LukeSAV/SDProject/ros_ws/src/rtk/src/ntripclient.cpp

/*
   NTRIP client for POSIX.
   $Id: ntripclient.c,v 1.51 2009/09/11 09:49:19 stoecker Exp $
   Copyright (C) 2003-2008 by Dirk Stöcker <soft@dstoecker.de>

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
 */

/**
 *
 *	@brief This contains the client code for running NTRIP corrections services with an RTK capable device.
 *			
 *	Currently supports Ubuntu devices running ROS. This device uses one USB port for NMEA read and RTCM write.
 *
 *	@author Luke Armbruster
 *
 *	@bug No known bugs.
 */



#include <ctype.h>
#include <getopt.h>
#include <stdio.h>
#include <stdlib.h>
#include <errno.h>
#include <string>
#include <time.h>
#include <chrono>
#include <vector>
#include <numeric>
#include <iostream>
#include <thread>
#include "ros/ros.h"
#include "std_msgs/String.h"
#include "sensor_msgs/NavSatFix.h"
#include "../include/NMEAData.h"
#include "rtk/HeadingSpeed.h"
#include "../include/serial.h"

typedef int sockettype;
#include <signal.h>
#include <fcntl.h>
#include <unistd.h>
#include <arpa/inet.h>
#include <sys/socket.h>
#include <netinet/in.h>
#include <netdb.h>

#define closesocket(sock)       close(sock)
#define ALARMTIME   (2*60)
#define myperror perror

/* The string, which is send as agent in HTTP request */
#define AGENTSTRING "NTRIP NtripClientPOSIX"
#define TIME_RESOLUTION 125

#define MAXDATASIZE 3000 /* max number of bytes we can get at once */

/* CVS revision and version */
static char revisionstr[] = "$Revision: 1.51 $";
static char datestr[]     = "$Date: 2018/12/12 09:49:19 $";

enum MODE { HTTP = 1, RTSP = 2, NTRIP1 = 3, AUTO = 4, UDP = 5, END };

/* */
std::mutex input_buf_lock;
static char input_buf[MAXDATASIZE * 2];
static char buf_to_send[MAXDATASIZE * 2];
static void handleIPConnection(sockettype sockfd);
static int numbytes = 0;

struct Args
{
	const char *server;
	const char *port;
	const char *user;
	const char *proxyhost;
	const char *proxyport;
	const char *password;
	const char *nmea;
	const char *data;
	int         bitrate;
	int         mode;

	int         udpport;
	int         initudp;
	enum SerialBaud baud;
	enum SerialDatabits databits;
	enum SerialStopbits stopbits;
	enum SerialParity parity;
	enum SerialProtocol protocol;
	const char *serdevice;
	const char *serlogfile;
	const char *nmea_usb;
	const char *rtcm_usb;
};

/* option parsing */
#ifdef NO_LONG_OPTS
#define LONG_OPT(a)
#else
#define LONG_OPT(a) a
static struct option opts[] = {
	{ "bitrate",    no_argument,       0, 'b'},
	{ "data",       required_argument, 0, 'd'}, /* compatibility */
	{ "mountpoint", required_argument, 0, 'm'},
	{ "initudp",    no_argument,       0, 'I'},
	{ "udpport",    required_argument, 0, 'P'},
	{ "server",     required_argument, 0, 's'},
	{ "password",   required_argument, 0, 'p'},
	{ "port",       required_argument, 0, 'r'},
	{ "proxyport",  required_argument, 0, 'R'},
	{ "proxyhost",  required_argument, 0, 'S'},
	{ "user",       required_argument, 0, 'u'},
	{ "nmea",       required_argument, 0, 'n'},
	{ "mode",       required_argument, 0, 'M'},
	{ "serdevice",  required_argument, 0, 'D'},
	{ "baud",       required_argument, 0, 'B'},
	{ "stopbits",   required_argument, 0, 'T'},
	{ "protocol",   required_argument, 0, 'C'},
	{ "parity",     required_argument, 0, 'Y'},
	{ "databits",   required_argument, 0, 'A'},
	{ "serlogfile", required_argument, 0, 'l'},
	{0,0,0,0}};
#endif
#define ARGOPT "-d:m:bhp:r:s:u:n:S:R:M:IP:D:B:T:C:Y:A:l:t:e:"

int stop = 0;
int sigstop = 0;
#ifdef __GNUC__
	static __attribute__ ((noreturn)) void sighandler_alarm(
			int sig __attribute__((__unused__)))
#else /* __GNUC__ */
static void sighandler_alarm(int sig)
#endif /* __GNUC__ */
{
	if(!sigstop)
		fprintf(stderr, "ERROR: more than %d seconds no activity\n", ALARMTIME);
	else
		fprintf(stderr, "ERROR: user break\n");
	exit(1);
}

#ifdef __GNUC__
static void sighandler_int(int sig) 
{
	fprintf(stderr, "ERROR: user break\n");
	exit(1);

}
#else /* __GNUC__ */
static void sighandler_alarm(int sig)
{
	sigstop = 1;
	alarm(2);
	stop = 1;
}
#endif /* __GNUC__ */

static void setargs(struct Args *args)
{
	args->server = "insert your ip address here";
	args->port = "10000";
	args->user = "insert your username here";
	args->password = "insert your password here";
	args->nmea = 0;
	args->data = "RTCM3_MAX";
	args->bitrate = 0;
	args->proxyhost = 0;
	args->proxyport = "2101";
	args->mode = NTRIP1;
	args->initudp = 0;
	args->udpport = 0;
	args->protocol = SPAPROTOCOL_NONE;
	args->parity = SPAPARITY_NONE;
	args->stopbits = SPASTOPBITS_1;
	args->databits = SPADATABITS_8;
	args->baud = SPABAUD_57600;
	args->serdevice = 0;
	args->serlogfile = 0;
}

static const char encodingTable [64] = {
	'A','B','C','D','E','F','G','H','I','J','K','L','M','N','O','P',
	'Q','R','S','T','U','V','W','X','Y','Z','a','b','c','d','e','f',
	'g','h','i','j','k','l','m','n','o','p','q','r','s','t','u','v',
	'w','x','y','z','0','1','2','3','4','5','6','7','8','9','+','/'
};

/* does not buffer overrun, but breaks directly after an error */
/* returns the number of required bytes */
static int encode(char *buf, int size, const char *user, const char *pwd)
{
	unsigned char inbuf[3];
	char *out = buf;
	int i, sep = 0, fill = 0, bytes = 0;

	while(*user || *pwd)
	{
		i = 0;
		while(i < 3 && *user) inbuf[i++] = *(user++);
		if(i < 3 && !sep)    {inbuf[i++] = ':'; ++sep; }
		while(i < 3 && *pwd)  inbuf[i++] = *(pwd++);
		while(i < 3)         {inbuf[i++] = 0; ++fill; }
		if(out-buf < size-1)
			*(out++) = encodingTable[(inbuf [0] & 0xFC) >> 2];
		if(out-buf < size-1)
			*(out++) = encodingTable[((inbuf [0] & 0x03) << 4)
				| ((inbuf [1] & 0xF0) >> 4)];
		if(out-buf < size-1)
		{
			if(fill == 2)
				*(out++) = '=';
			else
				*(out++) = encodingTable[((inbuf [1] & 0x0F) << 2)
					| ((inbuf [2] & 0xC0) >> 6)];
		}
		if(out-buf < size-1)
		{
			if(fill >= 1)
				*(out++) = '=';
			else
				*(out++) = encodingTable[inbuf [2] & 0x3F];
		}
		bytes += 4;
	}
	if(out-buf < size)
		*out = 0;
	return bytes;
}

static struct serial rtk_uart; // Serial connection (read/write at 57600)

int main(int argc, char **argv)
{
	ros::init(argc, argv, "rtk_gps_node");
	ros::NodeHandle nh;
	ros::Publisher gpgga_pub = nh.advertise<sensor_msgs::NavSatFix>("rtk_gpgga", 1000);
	ros::Publisher gpvtg_pub = nh.advertise<rtk::HeadingSpeed>("rtk_gpvtg", 1000);

	while(ros::ok()) {
		struct Args args;

		setbuf(stdout, 0);
		setbuf(stdin, 0);
		setbuf(stderr, 0);
		signal(SIGALRM,sighandler_alarm);
		signal(SIGINT,sighandler_int);
		alarm(ALARMTIME);
		setargs(&args);

		FILE *ser = 0;
		char nmeabuffer[200] = "$GPGGA,"; // Start string
		size_t nmeabufpos = 0;
		size_t nmeastarpos = 0;
		int sleeptime = 0;
		const char *rtk_uart_conn = SerialInit(&rtk_uart, "/dev/gps", SPABAUD_57600,
				args.stopbits, args.protocol, args.parity, args.databits, 1);
		
		if(rtk_uart_conn)
		{
			printf("Not connected to RTK device\n");
		}
		do {
			sockettype sockfd = 0;
			struct sockaddr_in their_addr;
			struct hostent *he;
			const char* server;
			const char* port;
			char* b;
			long in_i;
			long out_i;
			char output_buf[MAXDATASIZE];

			char read_buf[MAXDATASIZE];
			int readBytes = 0;

			server = args.server;
			printf("Server: %s\n", server);
			port = args.port;
			printf("Port: %s\n", port);
			memset(&their_addr, 0, sizeof(struct sockaddr_in));
			printf("Waiting for data...\n");


				auto start = std::chrono::system_clock::now();
				auto cur_time = start;
				std::chrono::duration<double> elapsed_time = std::chrono::duration<double>(10.0f); // Initially send message to caster

				std::thread ntrip_thread(handleIPConnection, sockfd); // Launch thread to handle communication with NTRIP server
				numbytes = 0;

				while(true) { // Read Caster data on socket continuously. Send GPGGA message every 5s.
					memset(read_buf, '\0', sizeof(read_buf)); // Clear the buffer
                    input_buf_lock.lock();
					readBytes = SerialRead(&rtk_uart, read_buf, MAXDATASIZE); // Receive any data from the UART hardware buffer
                    input_buf_lock.unlock();

					NMEAData::parseNMEA(read_buf, readBytes, gpgga_pub, gpvtg_pub); // Check the buffer for the relevant data

					cur_time = std::chrono::system_clock::now();
					elapsed_time = cur_time - start;
					//std::cout << elapsed_time.count() << std::endl;
					std::this_thread::sleep_for(std::chrono::milliseconds(900));
				}
				ntrip_thread.join();
			printf("Done\n");
			//
			sleep(1);
		} while(true);
		return 0;
	}
}

static void handleIPConnection(sockettype sockfd) {
	std::chrono::duration<double> debug_time = std::chrono::duration<double>(0.0f);
	char ip_recv_buf[MAXDATASIZE];
	int ip_recv_bytes = 0;

	while(true) {
		ip_recv_bytes = recv(sockfd, ip_recv_buf, MAXDATASIZE-1, 0); // Receive any RTCM data from caster
		if(ip_recv_bytes + numbytes > MAXDATASIZE) {
			ROS_ERROR("OVERRAN NTRIP BUFFER");
		}
		input_buf_lock.lock();
		memcpy(input_buf + numbytes, ip_recv_buf, ip_recv_bytes);
		numbytes += ip_recv_bytes;
		if(numbytes > 0) { // This should be the full blown RTCM3 message
			alarm(ALARMTIME); // Data has been received, reset the alarm
			SerialWrite(&rtk_uart, ip_recv_buf, numbytes);	
			numbytes = 0; // All buffer data was written
		}
		input_buf_lock.unlock();
		std::this_thread::sleep_for(std::chrono::milliseconds(500));
	}

}
