LukeSAV/SDProject/ros_ws/src/rtk/include/Landmark.h

#pragma once
#include <map>
#include <string>
#include <vector>
#include "Node.h"
class Landmark {
public: 
	Landmark();
	virtual ~Landmark();
	static std::string nearestLandmarkKey; // String key using unique identifier to the nearest landmark
	static std::string nearestLandmarkName;
	static std::map<std::string, Node> node_map;
	static std::map<std::string, std::pair<std::vector<std::string>, std::string>> way_map;
	
	static void setClosestLandmark();
};
